Krabbens/ledarray/esp/src/Decompressor.h

#pragma once
#include <Arduino.h>
#include <FastLED.h>
#include <lz4.h>
#include "Debug.h"
#include <cstring> 

#define BLOCK_SIZE 400
#define COLOR_BLOCK_SIZE BLOCK_SIZE * sizeof(CRGB)

class Decompressor
{
public:
    Decompressor();
    ~Decompressor() = default;

    static unsigned int palette[256][3];

    static CRGB getColor(int index)
    {
        return CRGB(palette[index][0], palette[index][1], palette[index][2]);
    }

    inline static void decompressColors(const uint8_t *input, CRGB *output, size_t inputSize, size_t outputCapacity, size_t& offset)
    {
        int start = micros();
        uint16_t size;
        size_t total_size = 0;

        while(total_size < outputCapacity){

            if (offset + sizeof(size) > inputSize) {
                offset = 0;
            }

            std::memcpy(&size, (input + offset), sizeof(size));
            offset += sizeof(size);

            if (offset + size > inputSize) {
                Debug::error("ERROR: Not enought data to decode. Offset: " + String(offset) + " Size: " + String(size));
                return;
            }

            int decompressed_size = LZ4_decompress_safe((char*)(input + offset), (char*)(bytes_buff), size, BLOCK_SIZE);
            
            if (decompressed_size != BLOCK_SIZE) {
                Debug::error("ERROR: Compression error! Offset: " + String(offset) + " Decompressed: "+ String(decompressed_size) + " / " + String(size));
                return;
            }

            if (total_size + decompressed_size > outputCapacity) {
                Debug::error("ERROR: Output buffer overload. Total size: " + String(total_size));
                return;
            }

            for(int j = 0; j < BLOCK_SIZE; ++j){
                output[j + total_size] = getColor(bytes_buff[j]);
            }

            offset += size;
            total_size += decompressed_size;
            ++frame_count;
        }
        Debug::info("OFFSET: " + String(offset) + ", INPUT SIZE: " + String(inputSize) + ", Frames: "+String(frame_count) + ", output: " + String((int)output));
        frame_count = 0;
    }

    inline static void decompress(const uint8_t *input, CRGB *output, size_t inputSize, size_t outputCapacity, size_t& offset)
    {
        int start = micros();
        uint16_t size;
        size_t total_size = 0;

        while(total_size < outputCapacity){

            if (offset + sizeof(size) > inputSize) {
                offset = 0;
            }

            std::memcpy(&size, (input + offset), sizeof(size));
            offset += sizeof(size);

            if (offset + size > inputSize) {
                Debug::error("ERROR: Not enought data to decode. Offset: " + String(offset) + " Size: " + String(size));
                return;
            }

            char* output_end = (char*)(output + total_size / sizeof(CRGB));

            int decompressed_size = LZ4_decompress_safe((char*)(input + offset), output_end, size, outputCapacity - total_size);
            
            if (decompressed_size != COLOR_BLOCK_SIZE) {
                Debug::error("ERROR: Compression error! Offset: " + String(offset) + " Decompressed: "+ String(decompressed_size) + " / " + String(size));
                return;
            }

            if (total_size + decompressed_size > outputCapacity) {
                Debug::error("ERROR: Output buffer overload. Total size: " + String(total_size));
                return;
            }

            offset += size;
            total_size += decompressed_size;
            ++frame_count;
        }
        frame_count = 0;
    }

private:
    inline static int frame_count = 0;
    inline static uint8_t bytes_buff[BLOCK_SIZE];
};

unsigned int Decompressor::palette[256][3] = {
    {0, 0, 0},
    {128, 0, 0},
    {0, 128, 0},
    {128, 128, 0},
    {0, 0, 128},
    {128, 0, 128},
    {0, 128, 128},
    {192, 192, 192},
    {128, 128, 128},
    {255, 0, 0},
    {0, 255, 0},
    {255, 255, 0},
    {0, 0, 255},
    {255, 0, 255},
    {0, 255, 255},
    {255, 255, 255},
    {0, 0, 0},
    {0, 0, 95},
    {0, 0, 135},
    {0, 0, 175},
    {0, 0, 215},
    {0, 0, 255},
    {0, 95, 0},
    {0, 95, 95},
    {0, 95, 135},
    {0, 95, 175},
    {0, 95, 215},
    {0, 95, 255},
    {0, 135, 0},
    {0, 135, 95},
    {0, 135, 135},
    {0, 135, 175},
    {0, 135, 215},
    {0, 135, 255},
    {0, 175, 0},
    {0, 175, 95},
    {0, 175, 135},
    {0, 175, 175},
    {0, 175, 215},
    {0, 175, 255},
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
};
